teamxlr8/WRO-Future-Engineers-2024/models/1.jpeg

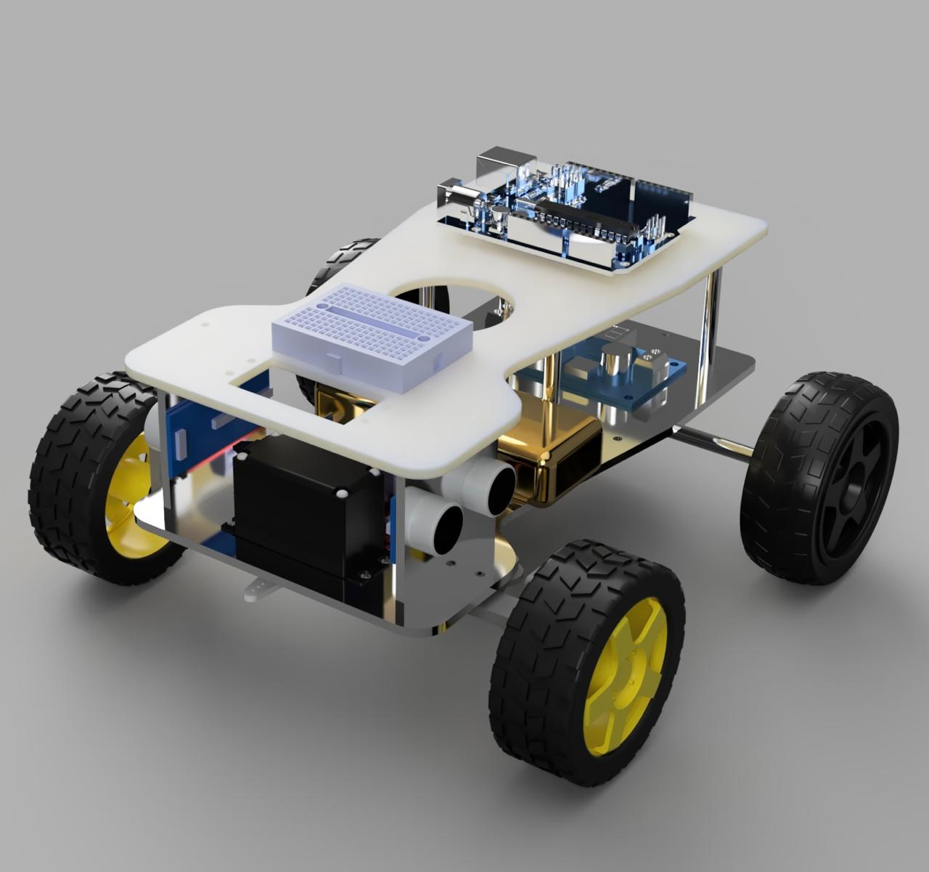
models/1.jpeg
