teamxlr8/WRO-Future-Engineers-2024/models/2.jpeg

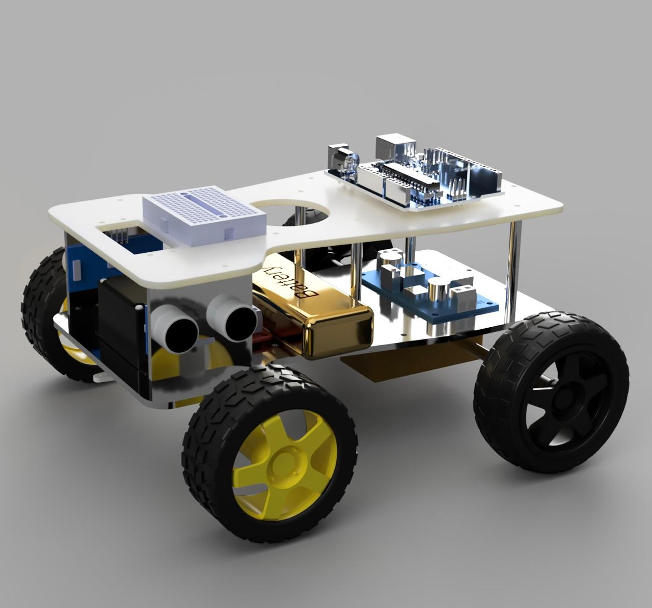
models/2.jpeg
