teamxlr8/WRO-Future-Engineers-2024/models/3.jpeg

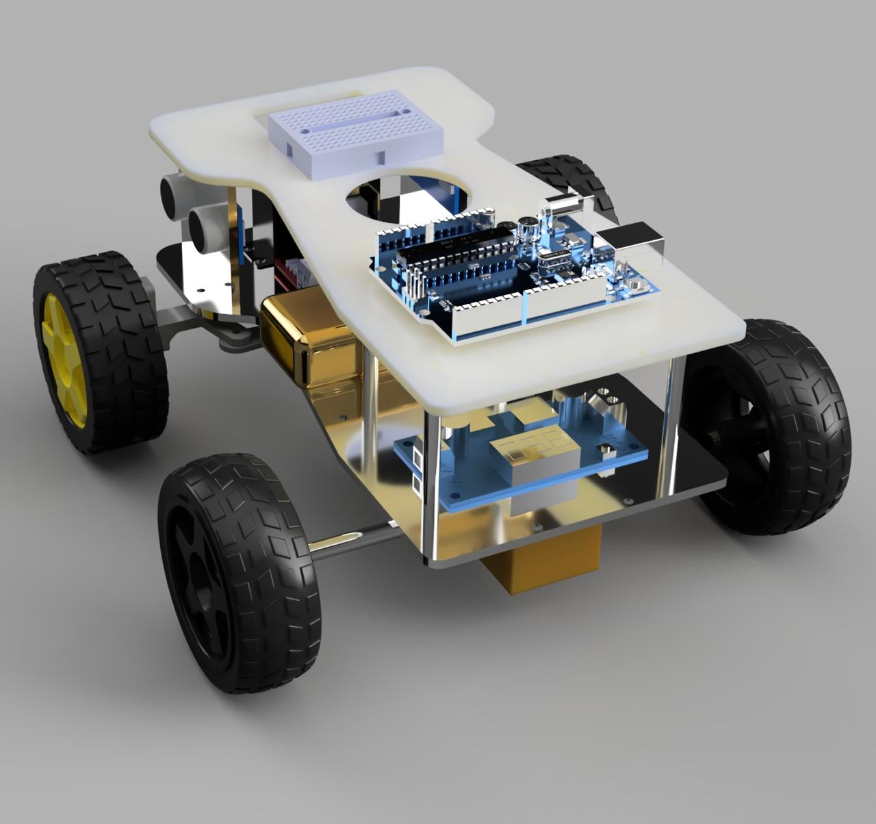
models/3.jpeg
