teamxlr8/WRO-Future-Engineers-2024/models/5.jpeg

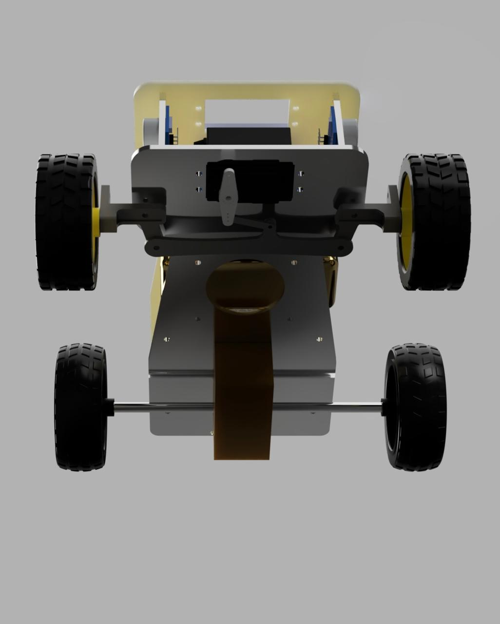
models/5.jpeg
