teamxlr8/WRO-Future-Engineers-2024/other/custom gear box/Updated Gear Box 1.jpg

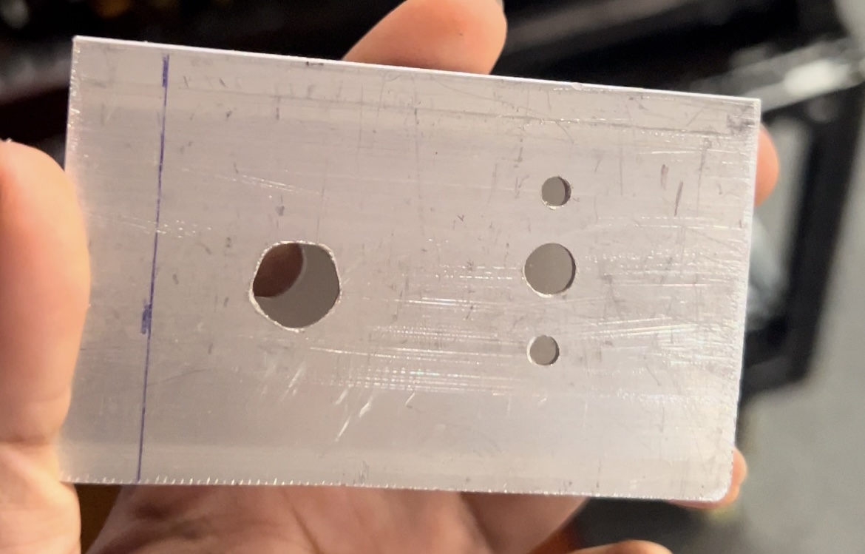
other/custom gear box/Updated Gear Box 1.jpg
