teamxlr8/WRO-Future-Engineers-2024/v-photos/Back.png

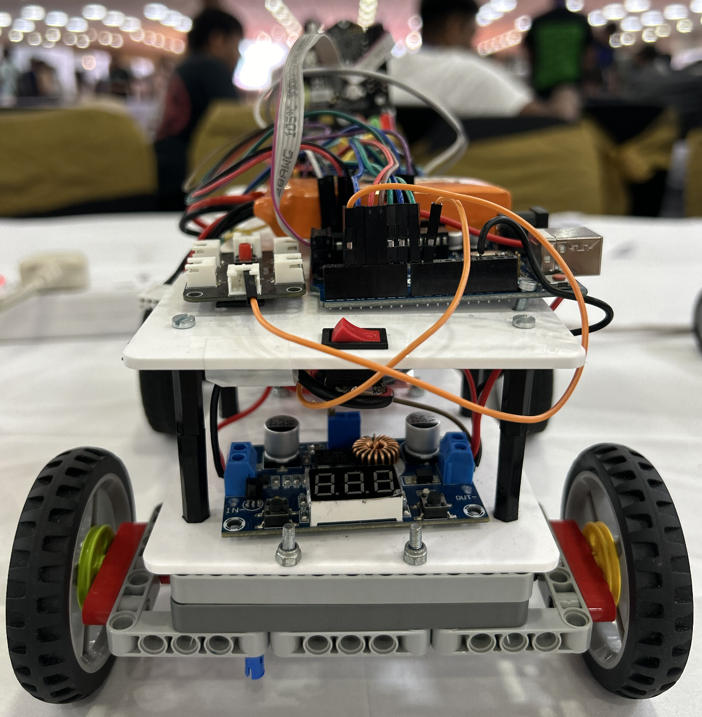
v-photos/Back.png
