teamxlr8/WRO-Future-Engineers-2024/v-photos/Front.png

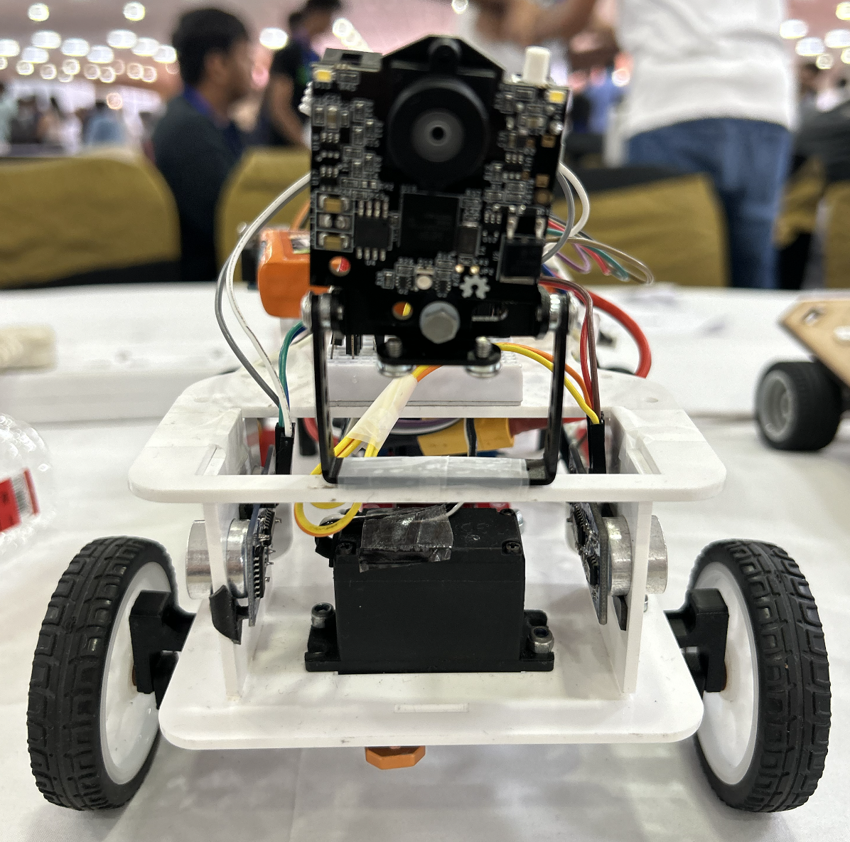
v-photos/Front.png
