teamxlr8/WRO-Future-Engineers-2024/v-photos/Left.png

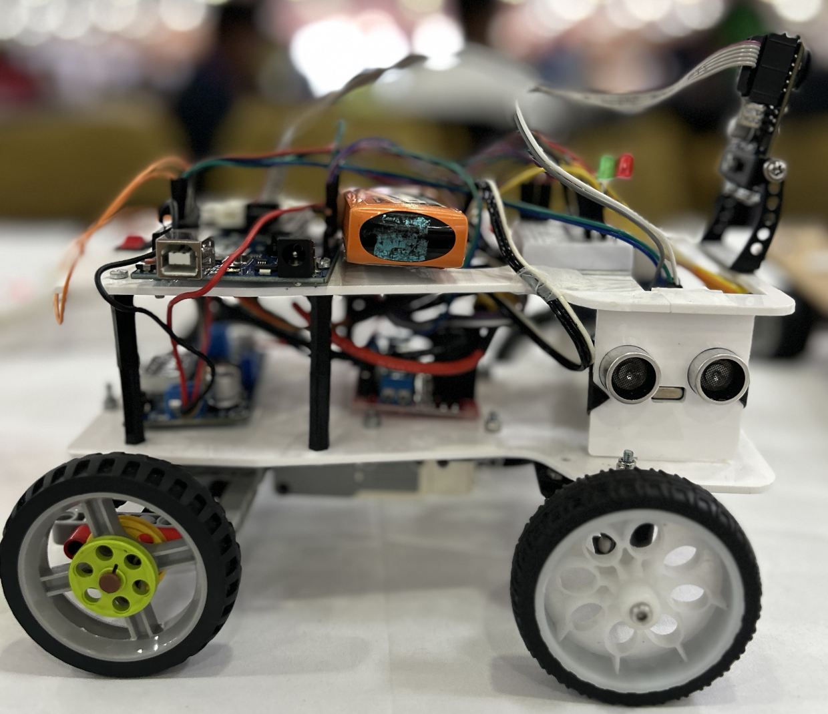
v-photos/Left.png
